makesaltlake/heimdall/hardware/shared/cots/pxc_1110581_10_00_LPC-2-5-2-ST-5-08_3D.stp

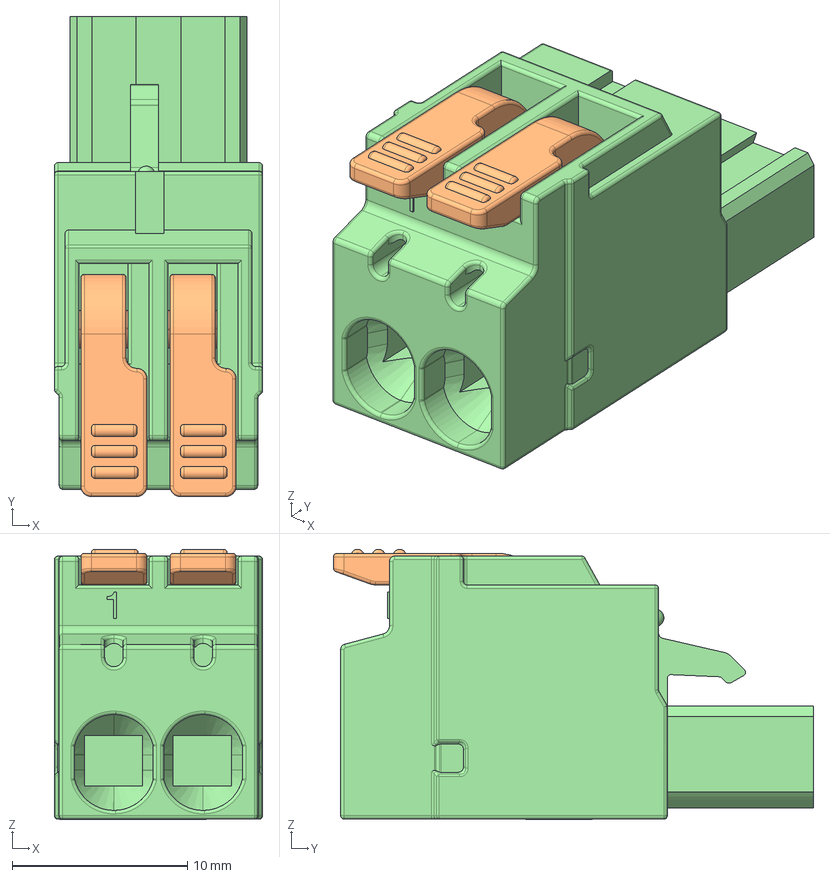
[picture p15: CAD file, 2026-03-23]
hardware/shared/cots/pxc_1110581_10_00_LPC-2-5-2-ST-5-08_3D.stp
11.9 x 27.4 x 15.4 mm
