makesaltlake/heimdall/hardware/shared/cots/CRJ024-1-TH.stp

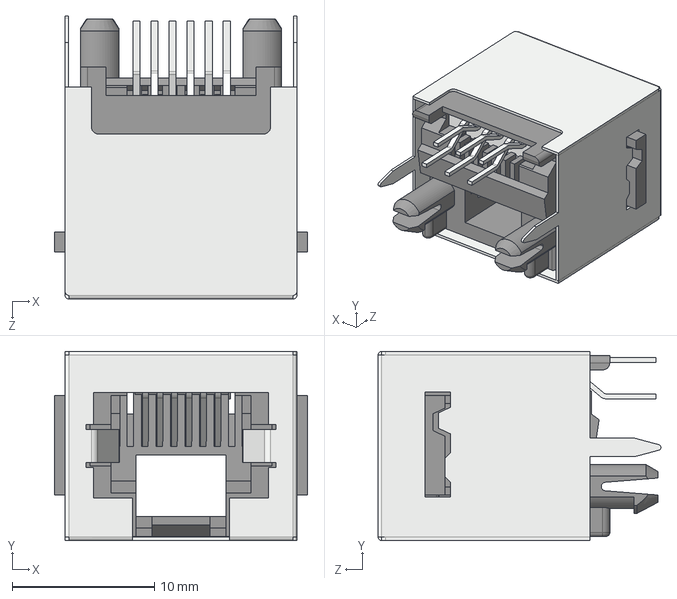
[picture p16: CAD file, 2026-01-07]
hardware/shared/cots/CRJ024-1-TH.stp
17.8 x 13.3 x 19.9 mm
