makesaltlake/heimdall/hardware/shared/cots/1991095.stp

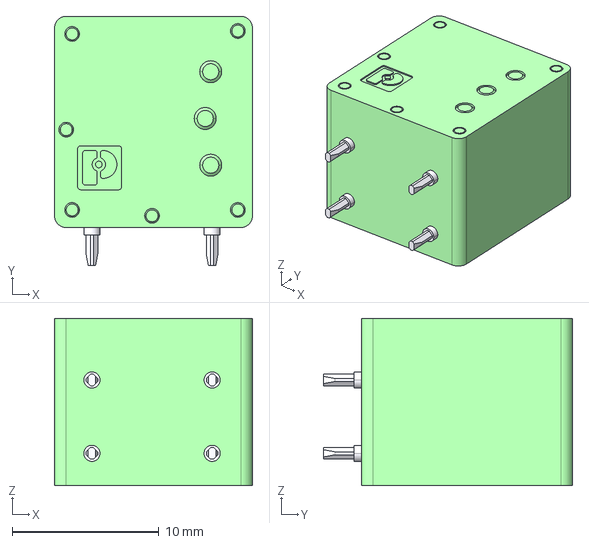
[picture p17: CAD file, 2026-01-07]
hardware/shared/cots/1991095.stp
13.5 x 17.0 x 11.4 mm
