makesaltlake/heimdall/hardware/shared/cots/CMT-1075-SMT-TR.stp

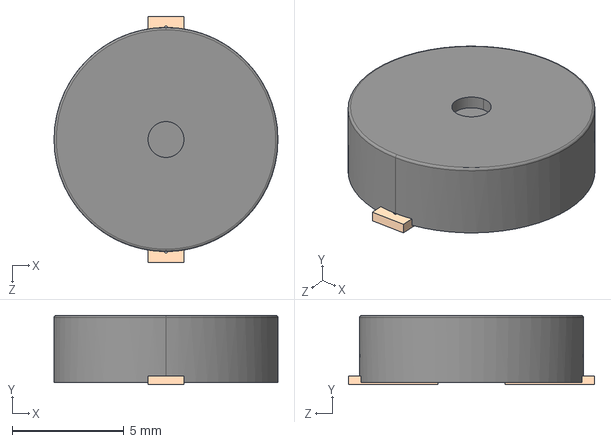
[picture p18: CAD file, 2025-10-26]
hardware/shared/cots/CMT-1075-SMT-TR.stp
10.0 x 3.10 x 11.0 mm
