makesaltlake/heimdall/firmware/common/tag.h

/*
 * Copyright (C) 2020 Rebecca Cran <rebecca@bsdio.com>.
 *
 */

 #ifndef FIRMWARE_COMMON_TAG_H__
 #define FIRMWARE_COMMON_TAG_H__

void tag_reader(void *param);
void tag_writer(void *param);

#endif /* FIRMWARE_COMMON_TAG_H__ */
