makesaltlake/heimdall/firmware/common/network.h

/*
 * Copyright (C) 2020 Rebecca Cran <rebecca@bsdio.com>.
 *
 */

void heimdall_setup_wifi(char *wifi_ssid, char *wifi_password);
void access_list_fetcher_thread(__attribute__((unused)) void *param);
void heimdall_setup_websocket(void);
bool send_badge_program(char *badge_token, char *name, int namelen);
void do_ota(void);
